ale1800/ESP-360-REMOTE/Images/without_top2.jpeg

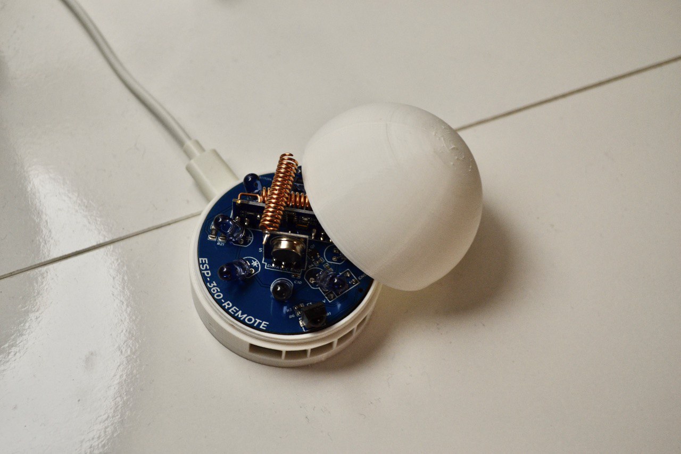
Images/without_top2.jpeg
