ale1800/ESP-360-REMOTE/Some remotes configurations/RF/Outon-Antys-Lastar-Lamp RF Remote/image (1).png

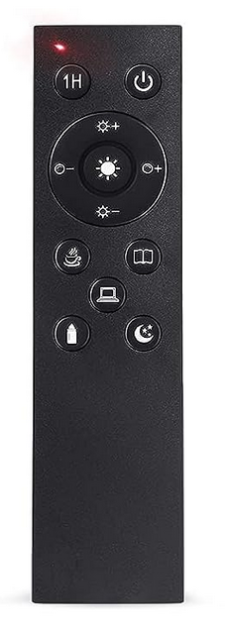
Some remotes configurations/RF/Outon-Antys-Lastar-Lamp RF Remote/image (1).png
