ale1800/ESP-360-REMOTE/Some remotes configurations/RF/RC-300 fireplace/515TkJNEh-L.jpg

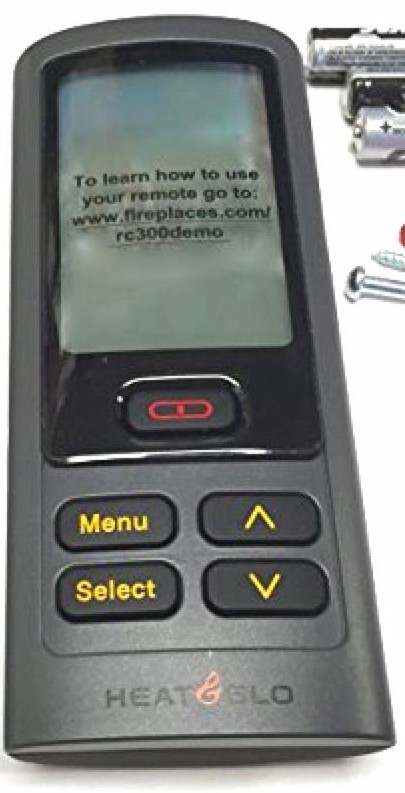
Some remotes configurations/RF/RC-300 fireplace/515TkJNEh-L.jpg
